OPEnSLab-OSU/WeatherChimes/Pictures/Figure 1_completedWeatherchimes.png

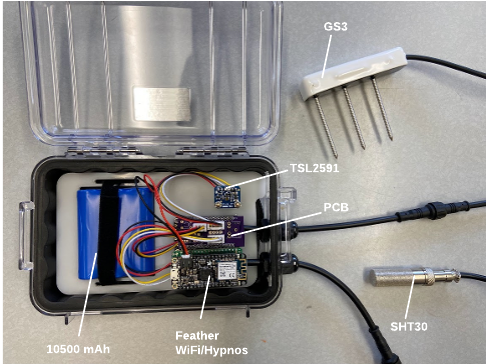
Pictures/Figure 1_completedWeatherchimes.png
