OPEnSLab-OSU/WeatherChimes/Pictures/Figure 3_Data handling flowchart for WeatherChimes.png

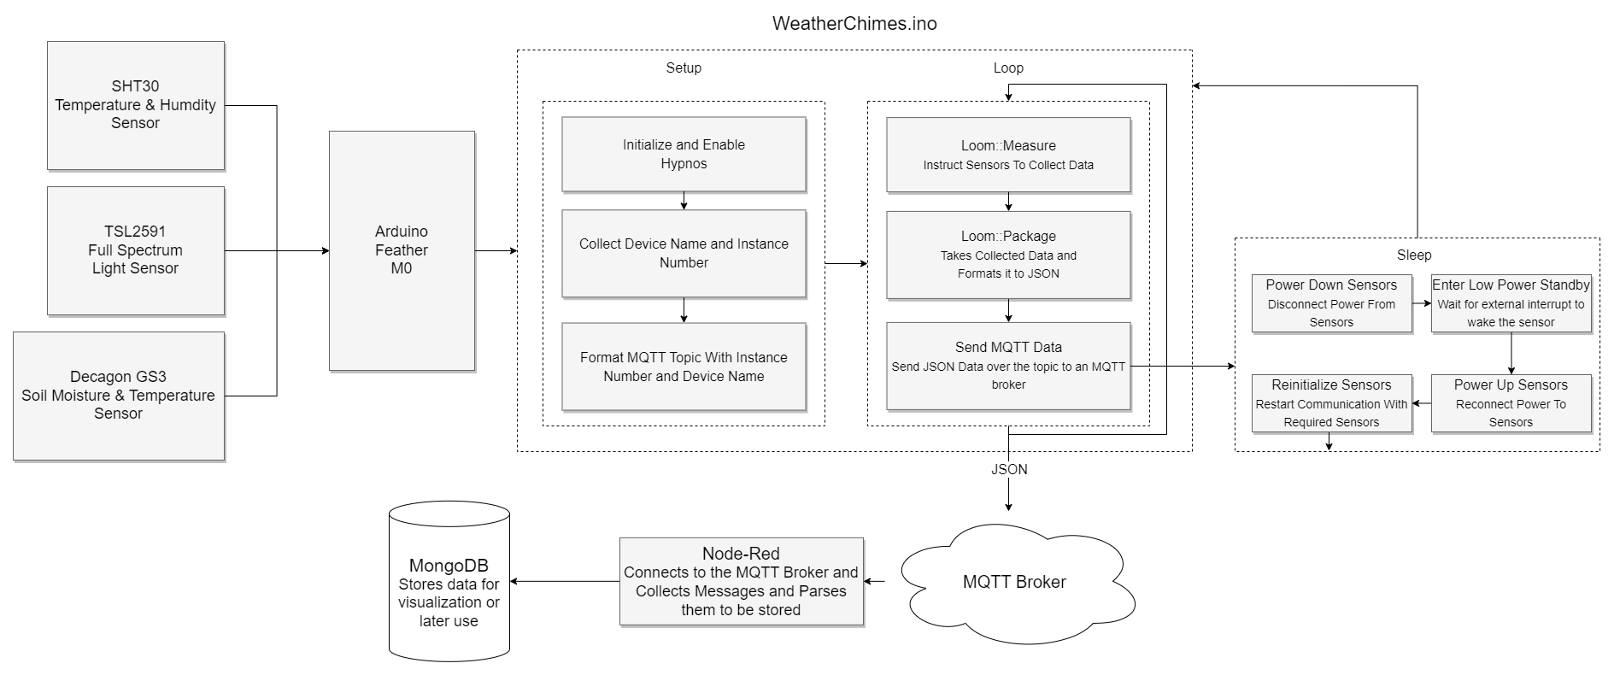
Pictures/Figure 3_Data handling flowchart for WeatherChimes.png
