OPEnSLab-OSU/WeatherChimes/Pictures/Figure 4_MongoDB Chime 1.PNG

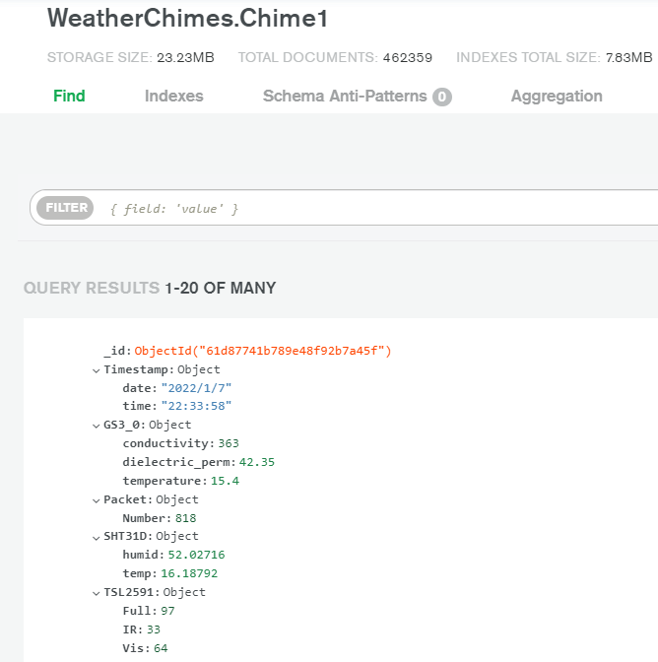
Pictures/Figure 4_MongoDB Chime 1.PNG
