OPEnSLab-OSU/WeatherChimes/Pictures/Figure 5_Cable Glands.jpg

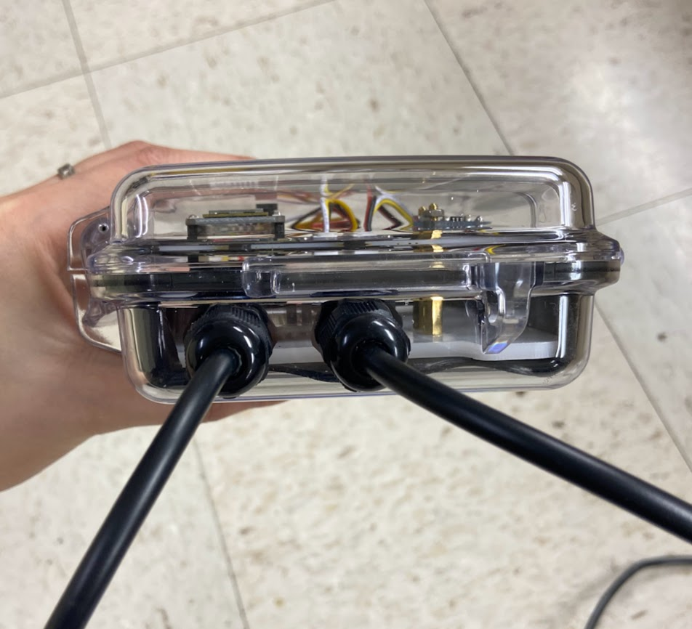
Pictures/Figure 5_Cable Glands.jpg
