OPEnSLab-OSU/WeatherChimes/Pictures/Figure 7_Doubler.jpg

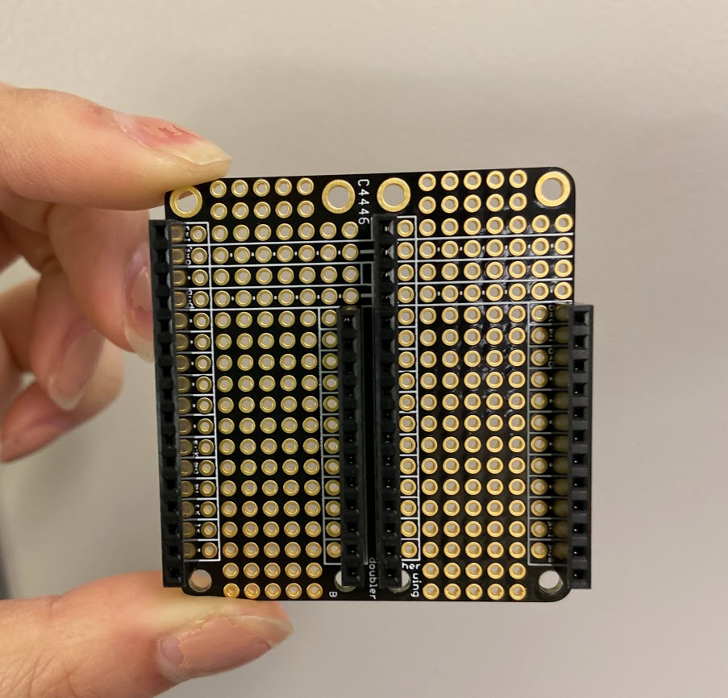
Pictures/Figure 7_Doubler.jpg
