OPEnSLab-OSU/WeatherChimes/Pictures/Figure 8_Doubler attachment.png

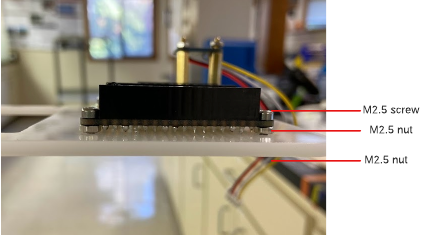
Pictures/Figure 8_Doubler attachment.png
