OPEnSLab-OSU/WeatherChimes/Pictures/Figure 10_PCB.png

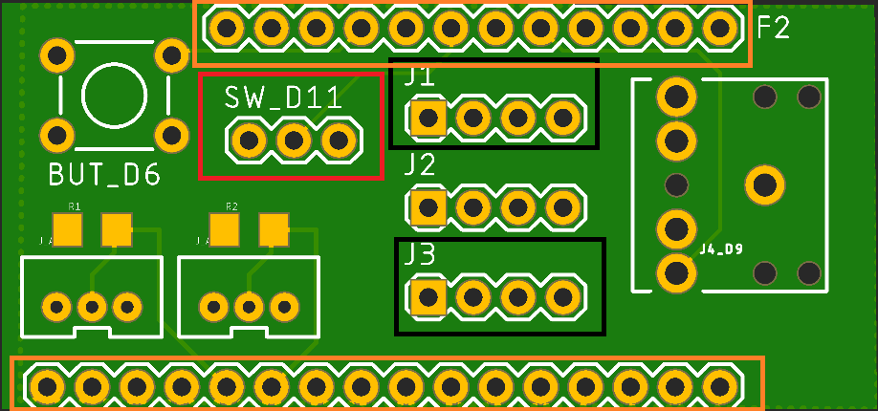
Pictures/Figure 10_PCB.png
