OPEnSLab-OSU/WeatherChimes/Pictures/Figure 11_GS3 to cable set.jpg

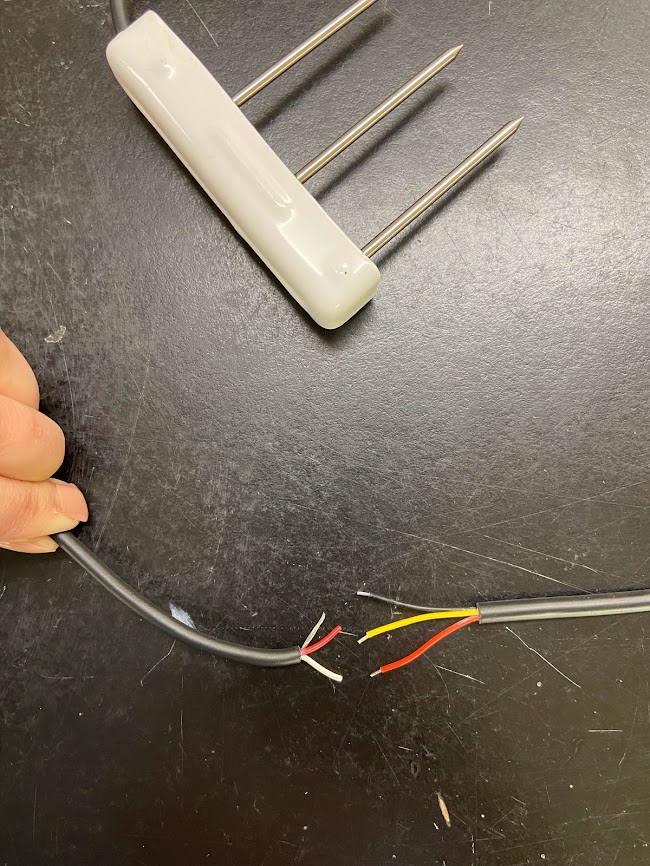
Pictures/Figure 11_GS3 to cable set.jpg
