OPEnSLab-OSU/WeatherChimes/Pictures/Figure 12_GS3_to_JST.jpg

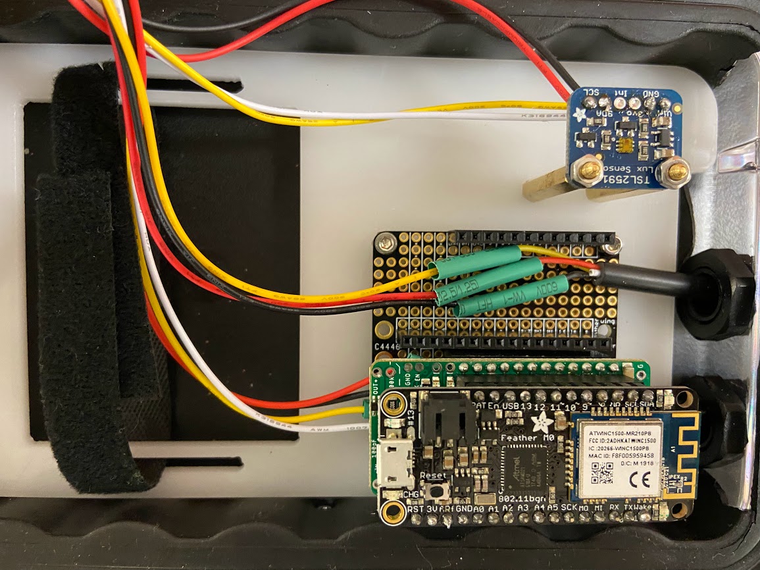
Pictures/Figure 12_GS3_to_JST.jpg
