OPEnSLab-OSU/WeatherChimes/Pictures/Figure 13_SHT_to_JST.jpg

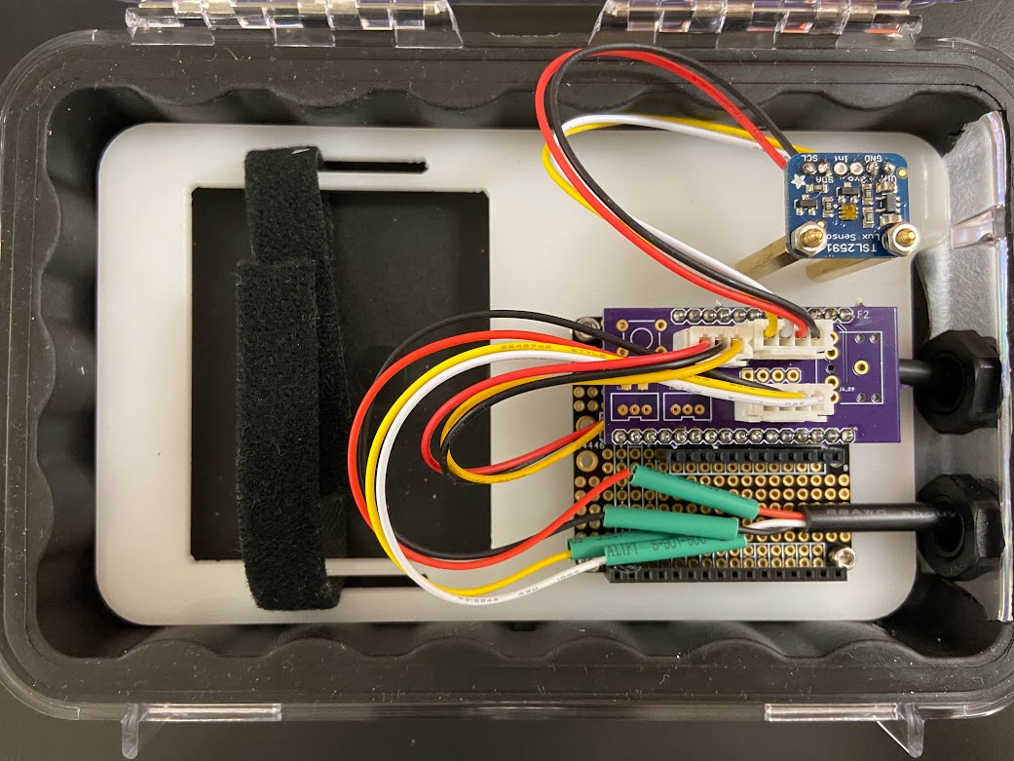
Pictures/Figure 13_SHT_to_JST.jpg
