OPEnSLab-OSU/WeatherChimes/Pictures/Figure 15_TSL on standoffs.jpg

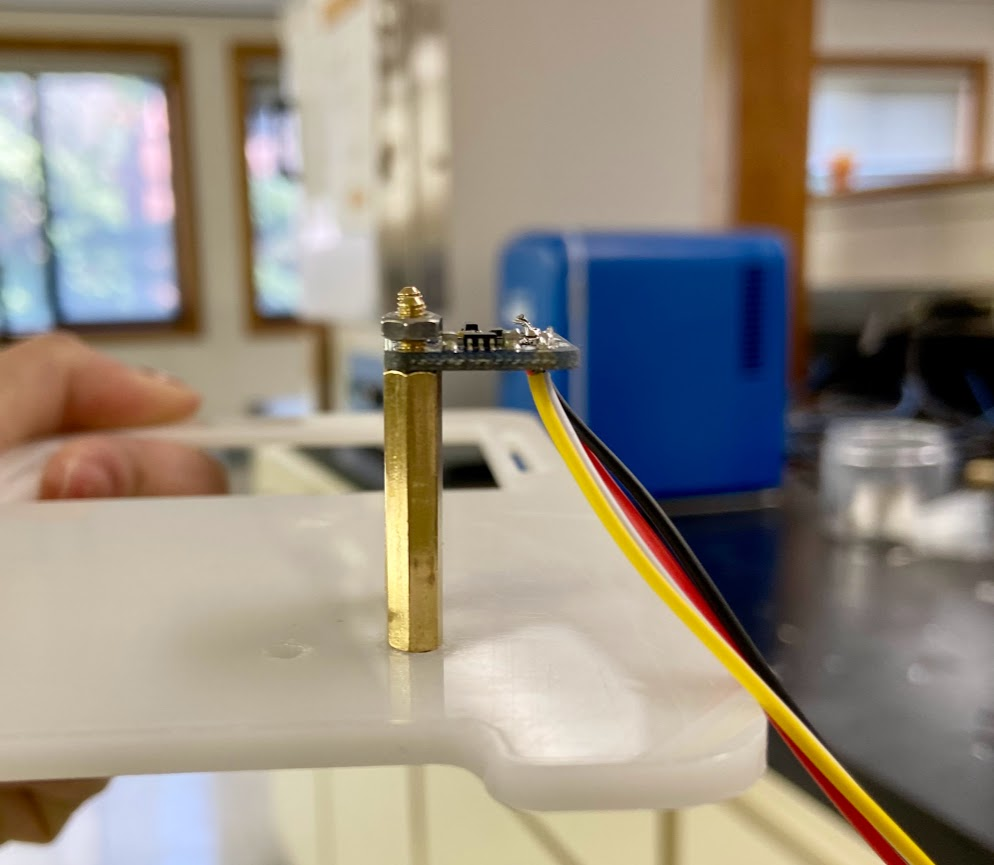
Pictures/Figure 15_TSL on standoffs.jpg
