OPEnSLab-OSU/WeatherChimes/Pictures/Figure 17_SHT-30 sensors zip-tied to tent stake.JPG

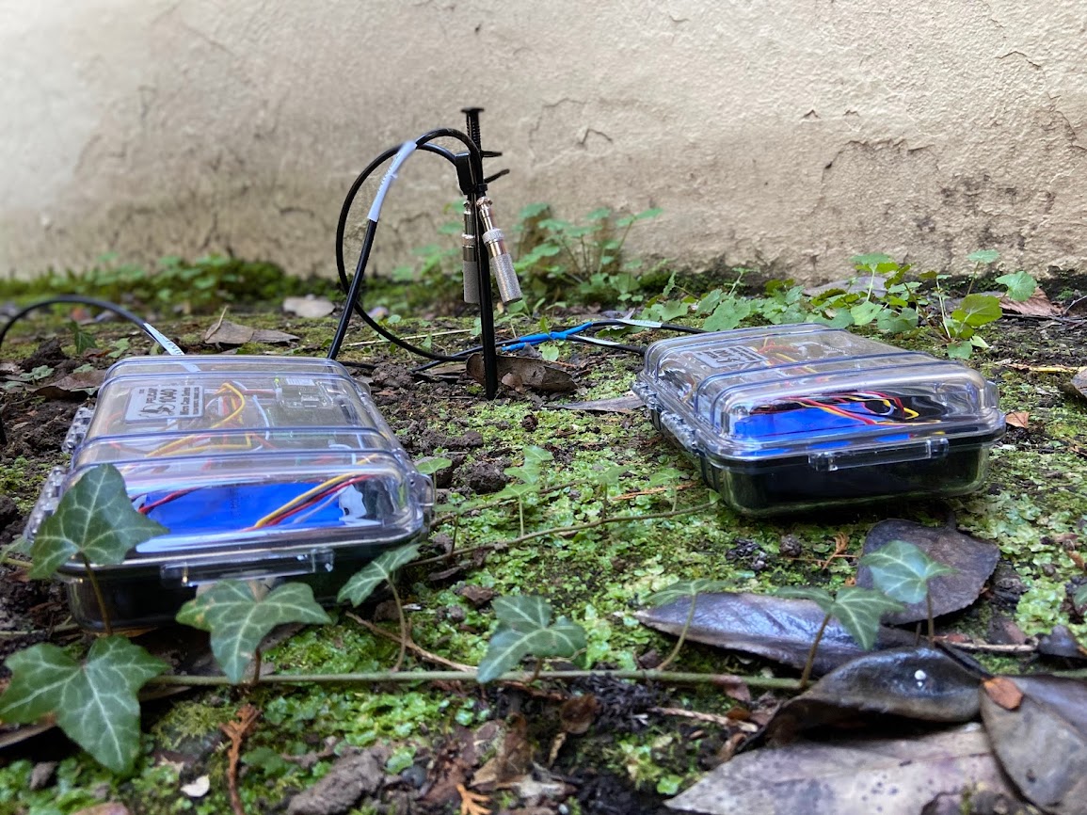
Pictures/Figure 17_SHT-30 sensors zip-tied to tent stake.JPG
