OPEnSLab-OSU/WeatherChimes/Pictures/Figure 18_Example connecting to MongoDB using Loom4Max Package.png

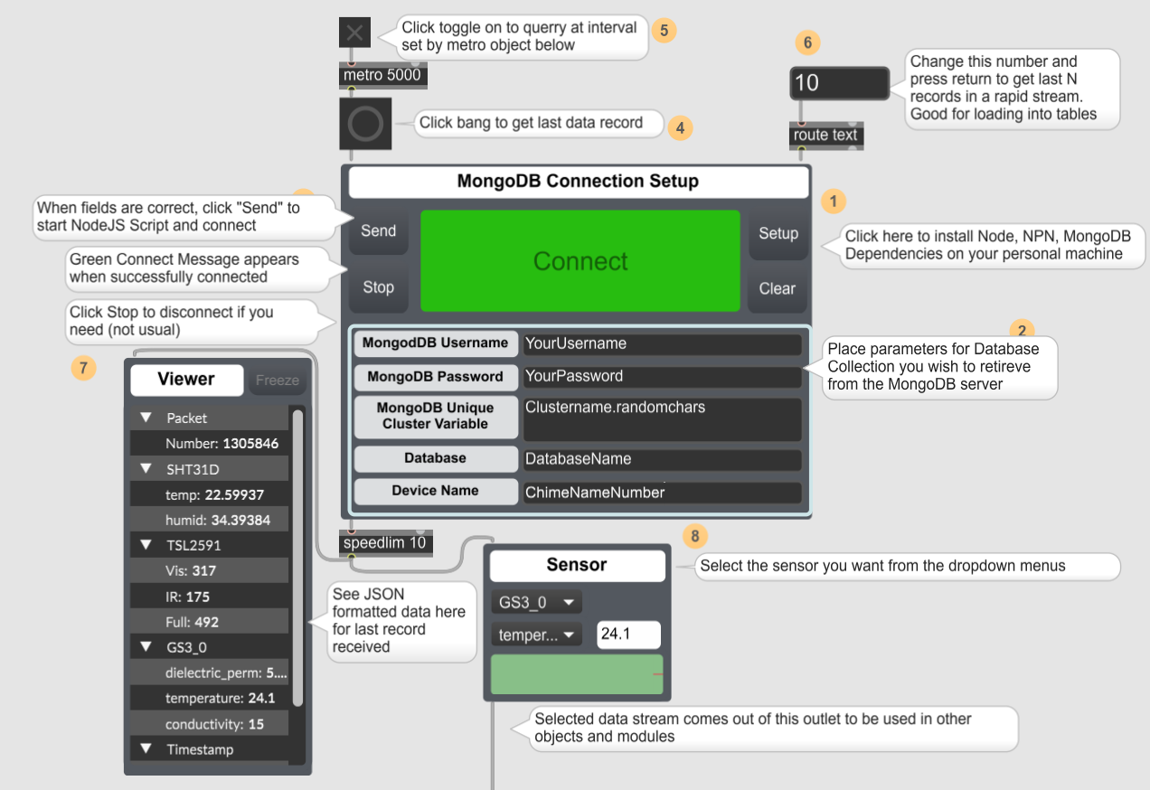
Pictures/Figure 18_Example connecting to MongoDB using Loom4Max Package.png
