OPEnSLab-OSU/WeatherChimes/Pictures/Figure 19_MongoDB chart displaying TSL2591 data.png

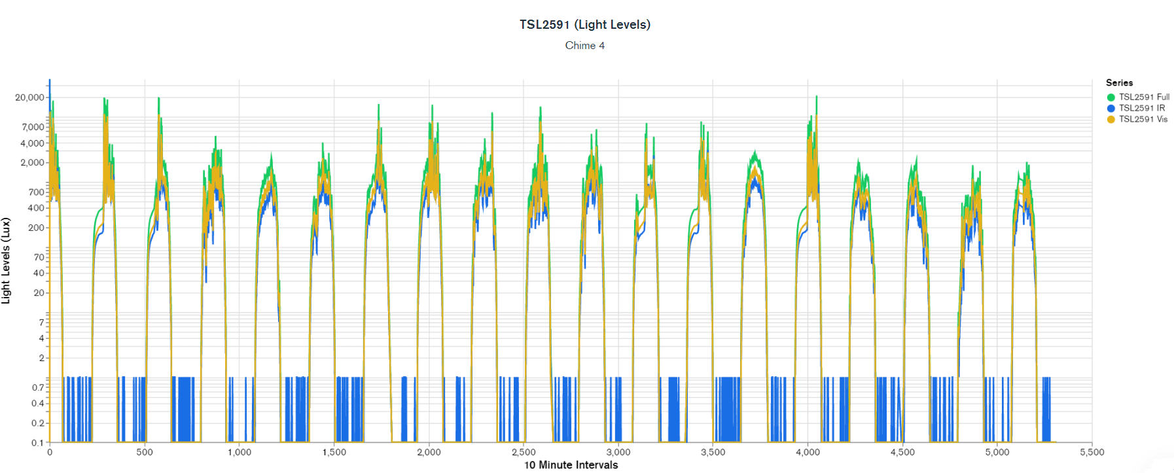
Pictures/Figure 19_MongoDB chart displaying TSL2591 data.png
