OPEnSLab-OSU/WeatherChimes/Pictures/Figure 20_MongoDB chart displaying GS3 VWC, Temp and SHT30 Temp.png

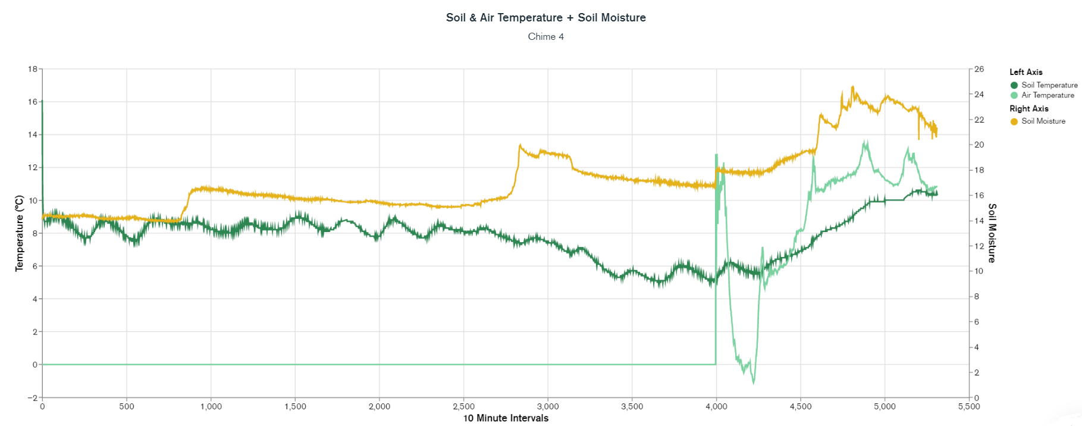
Pictures/Figure 20_MongoDB chart displaying GS3 VWC, Temp and SHT30 Temp.png
