OPEnSLab-OSU/WeatherChimes/Pictures/Figure 21_MongoDB chart displaying battery level.PNG

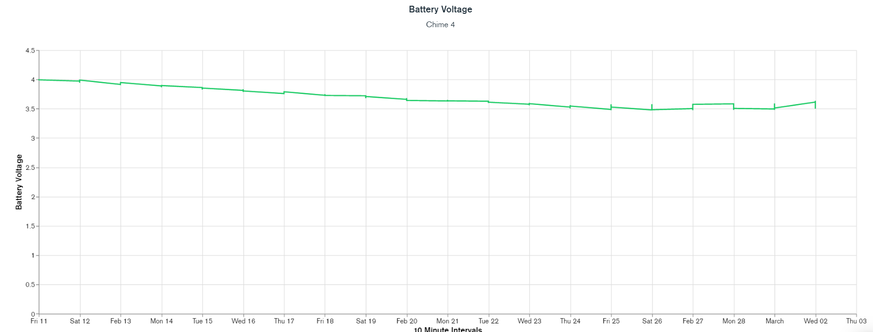
Pictures/Figure 21_MongoDB chart displaying battery level.PNG
