OPEnSLab-OSU/WeatherChimes/Pictures/Figure 22 Low and High temperature in Corvallis from Feb. 11 to Mar. 2.png

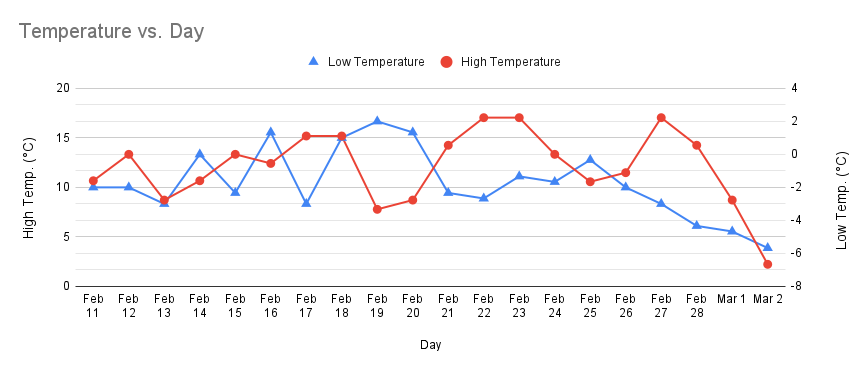
Pictures/Figure 22 Low and High temperature in Corvallis from Feb. 11 to Mar. 2.png
