OPEnSLab-OSU/WeatherChimes/Pictures/Figure 22_Electric Nature final project pt 2.PNG

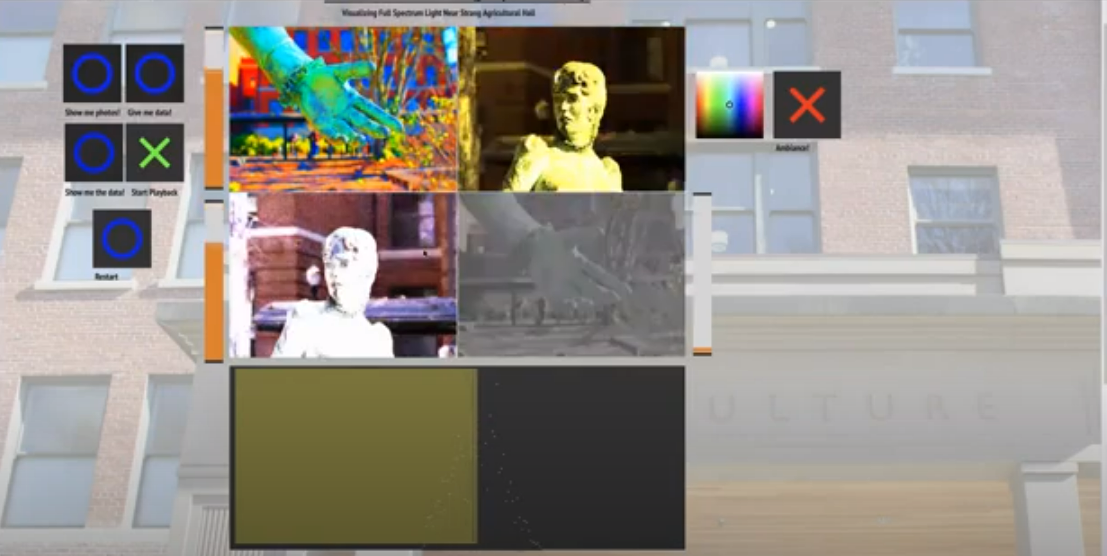
Pictures/Figure 22_Electric Nature final project pt 2.PNG
