OPEnSLab-OSU/WeatherChimes/Pictures/Figure 22_Electric Nature final project.png

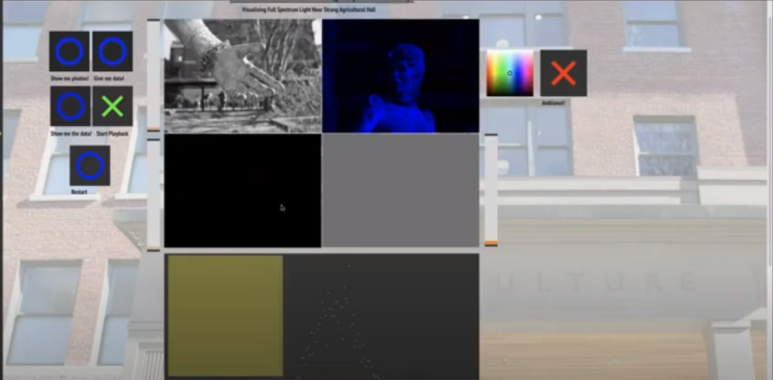
Pictures/Figure 22_Electric Nature final project.png
