OPEnSLab-OSU/WeatherChimes/Pictures/Figure 23_Fickle Nature interface.png

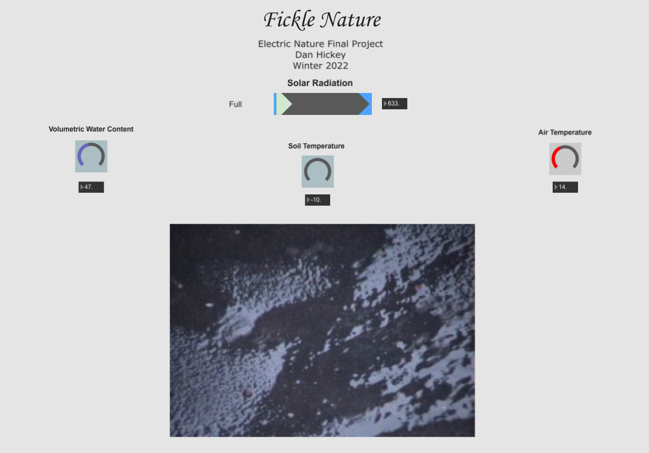
Pictures/Figure 23_Fickle Nature interface.png
