OPEnSLab-OSU/WeatherChimes/Pictures/Figure 26_Sitka.png

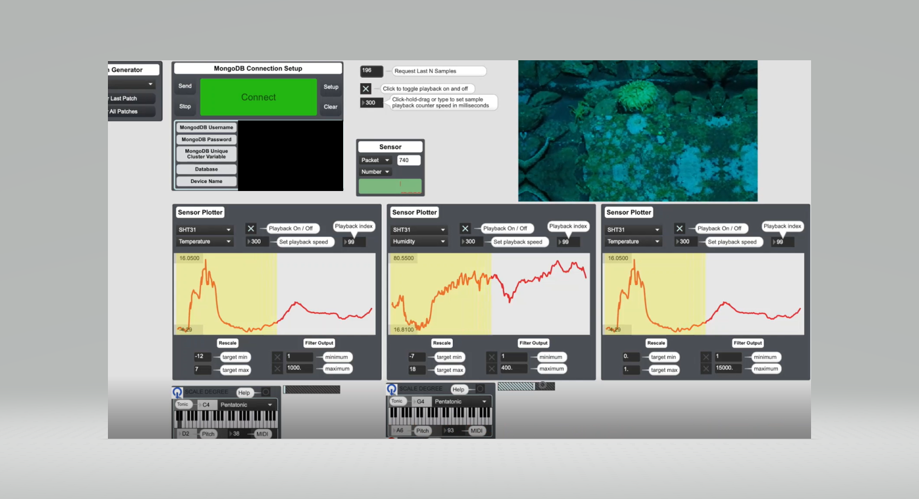
Pictures/Figure 26_Sitka.png
