OPEnSLab-OSU/WeatherChimes/Pictures/Figure 9_HypnosAssembly.png

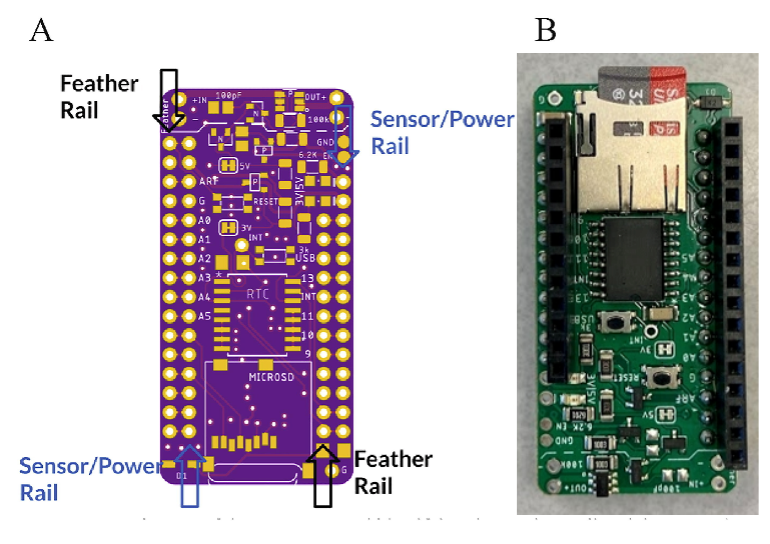
Pictures/Figure 9_HypnosAssembly.png
